Dr-CK/SimonSays/Schematic/SimonSays.kicad_pcb

## KiCad design hardware/circuit/kicad/zoomender.sch

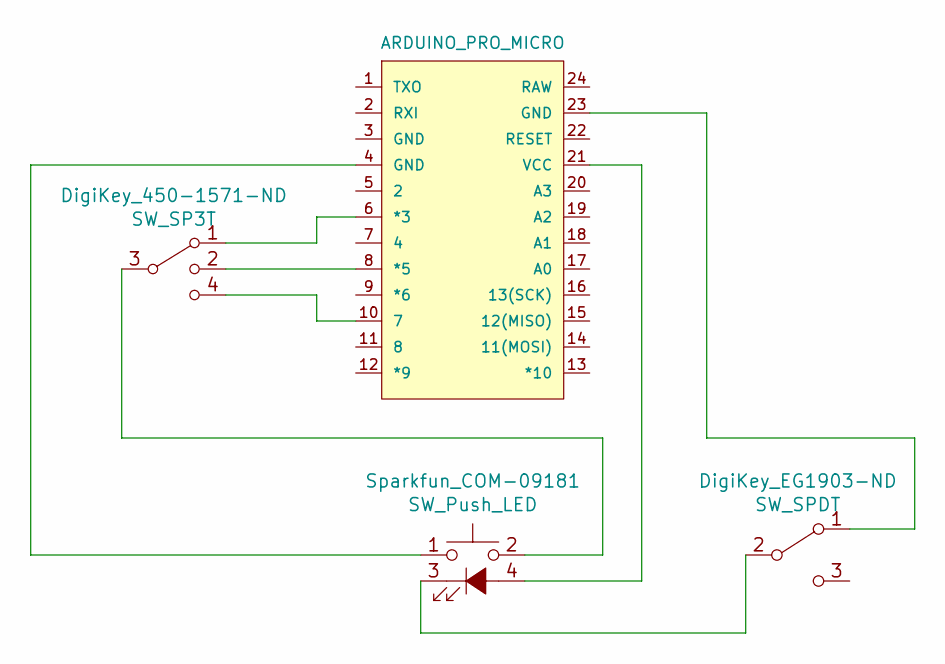
[picture p4: schematic zoomender.sch]

Parts:
B0: ARDUINO_PRO_MICRO; SPARKFUN_PRO_MICRO
DigiKey_450-1571-ND: SW_SP3T
DigiKey_EG1903-ND: SW_SPDT
Sparkfun_COM-09181: SW_Push_LED

Connections:
unnamed: B0.4 (GND), Sparkfun_COM-09181.1
unnamed: B0.6 (*3), DigiKey_450-1571-ND.1
unnamed: B0.8 (*5), DigiKey_450-1571-ND.2
unnamed: B0.10 (7), DigiKey_450-1571-ND.4
unnamed: B0.21 (VCC), Sparkfun_COM-09181.4 (A)
unnamed: B0.23 (GND), DigiKey_EG1903-ND.1 (A)
unnamed: DigiKey_450-1571-ND.3, Sparkfun_COM-09181.2
unnamed: DigiKey_EG1903-ND.2 (B), Sparkfun_COM-09181.3 (K)
